jsteinka05-ui/ESP32-Digital-Business-Card/firmware/main/slides.h

#ifndef SLIDES_H
#define SLIDES_H

#include <stddef.h>
#include <stdint.h>
#include "esp_err.h"

// Number of embedded slides in display order
size_t slides_count(void);

// Return the slide name or NULL for an invalid index
const char *slides_name(size_t index);

// Check every embedded image before displaying the first slide
esp_err_t slides_validate(void);

// Draw a slide without resetting the panel
esp_err_t slides_draw(size_t index);

// Copy a bounded rectangle into packed RGB888 rows
// Include the same QR colors used by full-screen drawing
esp_err_t slides_read_region(size_t index, int x, int y, int width, int height,
                            uint8_t *pixels, size_t length);

#endif // SLIDES_H
